ytmytm/C64-Keyboard/USB/SEEED/C128_keyboard_MT8816/PCB/kicad-c128keyb.kicad_sch

## KiCad design USB/SEEED/C128_keyboard_MT8816/PCB/kicad-c128keyb.kicad_sch (2022-05-27)

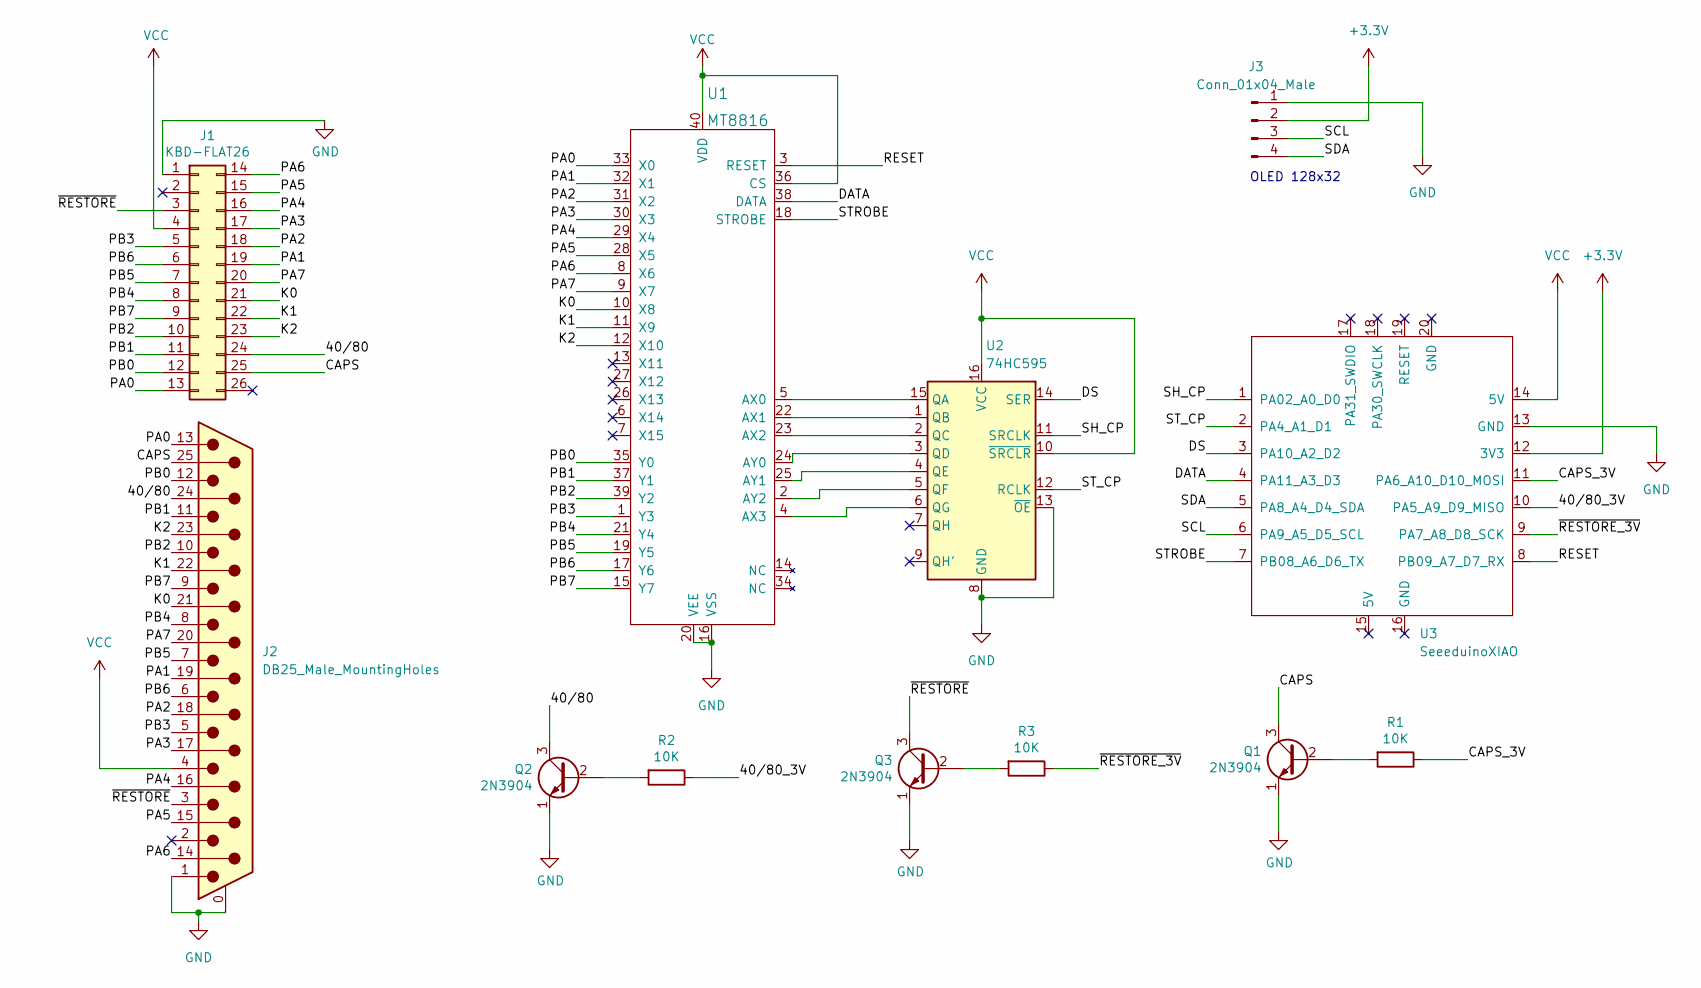
[picture p7: schematic kicad-c128keyb.kicad_sch]

Parts:
J1: KBD-FLAT26; PinHeader_2x13_P2.54mm_Vertical
J2: DB25_Male_MountingHoles; DSUB-25_Male_Horizontal_P2.77x2.84mm_EdgePinOffset4.94mm_Ho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
J3: Conn_01x04_Male; PinHeader_1x04_P2.54mm_Vertical
Q1, Q2, Q3: 2N3904; TO-92_Inline
R1, R2, R3: 10K; R_Axial_DIN0207_L6.3mm_D2.5mm_P7.62mm_Horizontal
U1: MT8816; DIP-40_W15.24mm_Socket
U2: 74HC595; DIP-16_W7.62mm_Socket
U3: SeeeduinoXIAO; Seeeduino XIAO-MOUDLE14P-2.54-21X17.8MM

Connections:
40/80: J1.24, J2.24, Q2.3 (C)
40/80_3V: R2.1, U3.10 (PA5_A9_D9_MISO)
+3.3V: J3.2, U3.12 (3V3)
CAPS: J1.25, J2.25, Q1.3 (C)
CAPS_3V: R1.1, U3.11 (PA6_A10_D10_MOSI)
DATA: U1.38 (DATA), U3.4 (PA11_A3_D3)
DS: U2.14 (SER), U3.3 (PA10_A2_D2)
GND: J1.1, J2.0 (PAD), J2.1, J3.1, Q1.1 (E), Q2.1 (E), Q3.1 (E), U1.16 (VSS), U1.20 (VEE), U2.8 (GND), U2.13 (~OE), U3.13 (GND)
K0: J1.21, J2.21, U1.10 (X8)
K1: J1.22, J2.22, U1.11 (X9)
K2: J1.23, J2.23, U1.12 (X10)
unnamed: Q1.2 (B), R1.2
unnamed: Q2.2 (B), R2.2
unnamed: Q3.2 (B), R3.2
unnamed: U1.2 (AY2), U2.5 (QF)
unnamed: U1.4 (AX3), U2.6 (QG)
unnamed: U1.5 (AX0), U2.15 (QA)
unnamed: U1.22 (AX1), U2.1 (QB)
unnamed: U1.23 (AX2), U2.2 (QC)
unnamed: U1.24 (AY0), U2.3 (QD)
unnamed: U1.25 (AY1), U2.4 (QE)
PA0: J1.13, J2.13, U1.33 (X0)
PA1: J1.19, J2.19, U1.32 (X1)
PA2: J1.18, J2.18, U1.31 (X2)
PA3: J1.17, J2.17, U1.30 (X3)
PA4: J1.16, J2.16, U1.29 (X4)
PA5: J1.15, J2.15, U1.28 (X5)
PA6: J1.14, J2.14, U1.8 (X6)
PA7: J1.20, J2.20, U1.9 (X7)
PB0: J1.12, J2.12, U1.35 (Y0)
PB1: J1.11, J2.11, U1.37 (Y1)
PB2: J1.10, J2.10, U1.39 (Y2)
PB3: J1.5, J2.5, U1.1 (Y3)
PB4: J1.8, J2.8, U1.21 (Y4)
PB5: J1.7, J2.7, U1.19 (Y5)
PB6: J1.6, J2.6, U1.17 (Y6)
PB7: J1.9, J2.9, U1.15 (Y7)
RESET: U1.3 (RESET), U3.8 (PB09_A7_D7_RX)
SCL: J3.3, U3.6 (PA9_A5_D5_SCL)
SDA: J3.4, U3.5 (PA8_A4_D4_SDA)
SH_CP: U2.11 (SRCLK), U3.1 (PA02_A0_D0)
STROBE: U1.18 (STROBE), U3.7 (PB08_A6_D6_TX)
ST_CP: U2.12 (RCLK), U3.2 (PA4_A1_D1)
VCC: J1.4, J2.4, U1.36 (CS), U1.40 (VDD), U2.10 (~SRCLR), U2.16 (VCC), U3.14 (5V)
~RESTORE_3V: R3.1, U3.9 (PA7_A8_D8_SCK)
~RESTORE: J1.3, J2.3, Q3.3 (C)

Notes on the sheet:
OLED 128x32
